peterdn/ttrpg-hex-map-console/firmware/assets/blacktower.png

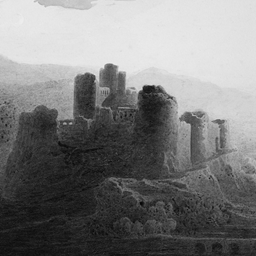
firmware/assets/blacktower.png
